lewispg228/headsupleds/HARDWARE/Right_Bar/drawing.bmp

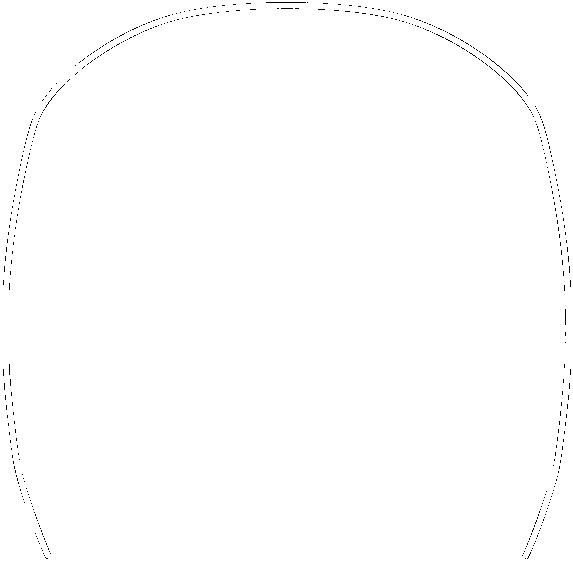
HARDWARE/Right_Bar/drawing.bmp
